akuker/SuperUPS/stm8_controller/inc/power_control.h

//---------------------------------------------------------------------------
//
//	Raspberry Pi SuperUPS
//
//	Copyright (C) 2020 Scott Baker
//	Copyright (C) 2022 akuker
//
//	[ Mosfet Handler ]
//
//---------------------------------------------------------------------------

#pragma once

void pwr_ctrl_step();
void power_control_init();
