akuker/SuperUPS/stm8_controller/src/adc_utilities.c

//---------------------------------------------------------------------------
//
//	Raspberry Pi SuperUPS
//
//	Copyright (C) 2020 Scott Baker
//	Copyright (C) 2022 akuker
//
//	[ ADC Utilities ]
//
//---------------------------------------------------------------------------
#include <stdint.h>
#include <stm8s_adc1.h>
#include "adc_utilities.h"
#include "i2c_register_data.h"

#define MAX_ADC_SAMPLES 8

#define GET_ON_THRESH uint8_t(VCONV_DIG(ON_THRESH_DESIRED))
#define GET_POWERUP_THRESH uint8_t(VCONV_DIG(POWERUP_THRESH_DESIRED))
#define GET_OFF_THRESH uint8_t(VCONV_DIG(OFF_THRESH_DESIRED))
#define GET_SHUTDOWN_THRESH uint8_t(VCONV_DIG(SHUTDOWN_THRESH_DESIRED))

static uint8_t sample_ptr = 0;
static uint8_t num_samples = 0;
static uint16_t vin_samples[MAX_ADC_SAMPLES];
static uint16_t vups_samples[MAX_ADC_SAMPLES];
static uint16_t vout_samples[MAX_ADC_SAMPLES];

static uint8_t computeAverage(uint16_t *samples)
{
    uint32_t accum = 0;
    uint8_t i;
    for (i = 0; i < num_samples; i++)
    {
        accum = accum + (uint32_t)samples[i];
    }

    uint32_t average = accum / num_samples;
    return (uint8_t)((average >> 2) & 0xFF);
}

//---------------------------------------------------------------------------
// Based upon:
// https://circuitdigest.com/microcontroller-projects/adc-on-stm8s-using-c-compiler-reading-multiple-adc-values-and-displaying-on-lcd
//---------------------------------------------------------------------------
static uint16_t read_adc(ADC1_Channel_TypeDef ADC_Channel_Number)
{
    ADC1_DeInit();
    ADC1_Init(ADC1_CONVERSIONMODE_CONTINUOUS,
              ADC_Channel_Number,
              ADC1_PRESSEL_FCPU_D18,
              ADC1_EXTTRIG_TIM,
              DISABLE,
              ADC1_ALIGN_RIGHT,
              ADC1_SCHMITTTRIG_ALL,
              DISABLE);
    ADC1_Cmd(ENABLE);
    ADC1_StartConversion();
    while (ADC1_GetFlagStatus(ADC1_FLAG_EOC) == RESET)
        ;
    uint16_t result = ADC1_GetConversionValue();
    ADC1_ClearFlag(ADC1_FLAG_EOC);
    ADC1_DeInit();

    return result;
}

void adc_init()
{
    i2c_register_values[I2C_ADC_VOLTAGE_IN] = 0;
    i2c_register_values[I2C_ADC_SUPER_CAP_VOLTAGE] = 0;
    i2c_register_values[I2C_ADC_VOLTAGE_OUT] = 0;
    // Enable Peripheral Clock for ADC
    CLK_PeripheralClockConfig(CLK_PERIPHERAL_ADC, ENABLE);
}

void adc_step()
{
    vin_samples[sample_ptr] = read_adc(ADC1_CHANNEL_4);
    vups_samples[sample_ptr] = read_adc(ADC1_CHANNEL_3);
    vout_samples[sample_ptr] = read_adc(ADC1_CHANNEL_2);
    sample_ptr = (sample_ptr + 1) % MAX_ADC_SAMPLES;
    num_samples++;
    if (num_samples > MAX_ADC_SAMPLES)
    {
        num_samples = MAX_ADC_SAMPLES;
    }

    // Only update the global values if we're NOT in test mode
    if (i2c_register_values[I2C_TEST_MODE_ENABLE] == 0)
    {
        i2c_register_values[I2C_ADC_VOLTAGE_IN] = computeAverage(vin_samples);
        i2c_register_values[I2C_ADC_SUPER_CAP_VOLTAGE] = computeAverage(vups_samples);
        i2c_register_values[I2C_ADC_VOLTAGE_OUT] = computeAverage(vout_samples);
    }
}
