akuker/SuperUPS/stm8_controller/inc/timer4_utilities.h

//---------------------------------------------------------------------------
//
//	Raspberry Pi SuperUPS
//
//	Copyright (C) 2020 Scott Baker
//	Copyright (C) 2022 akuker
//
//	[ Timer utilities ]
//
//---------------------------------------------------------------------------

#pragma once

void timer_init();

void delay_ms(unsigned long count);
void delay_us(unsigned long count);
